morganoliviaevans/cs-147-project/3d-housing/screenshots/Screenshot 2024-11-24 172925.png

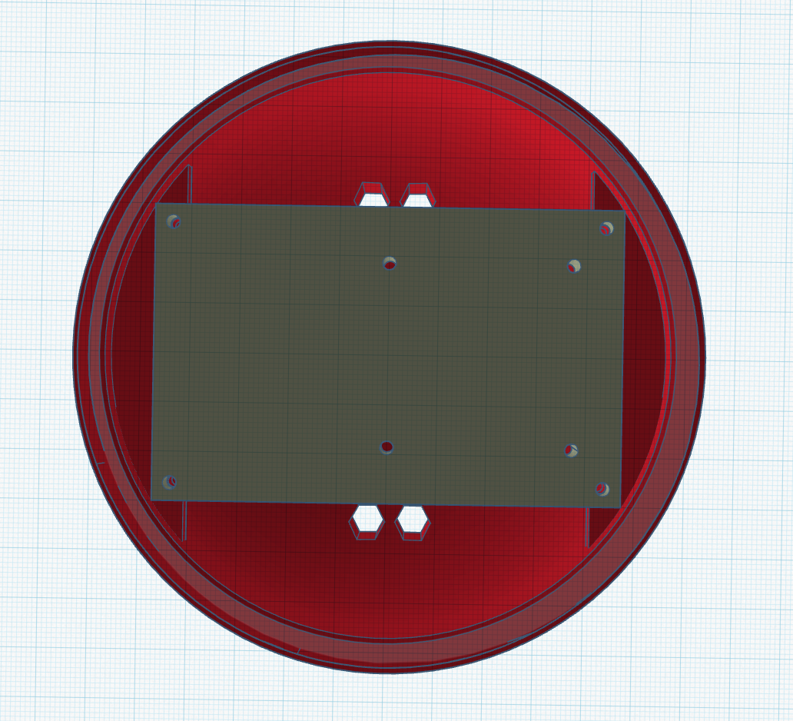
3d-housing/screenshots/Screenshot 2024-11-24 172925.png
