morganoliviaevans/cs-147-project/data-sheets/TTGO-data-sheet.png

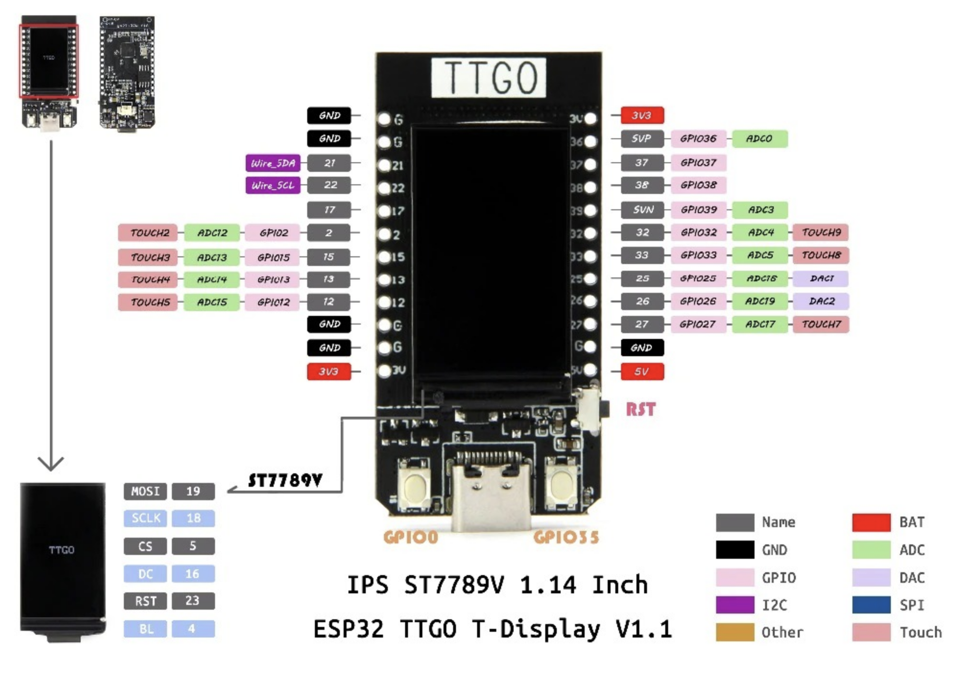
data-sheets/TTGO-data-sheet.png
