morganoliviaevans/cs-147-project/images/aws-graph.png

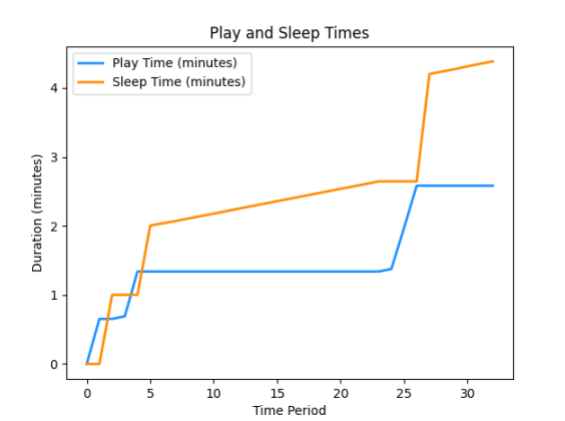
images/aws-graph.png
