morganoliviaevans/cs-147-project/images/aws-off.png

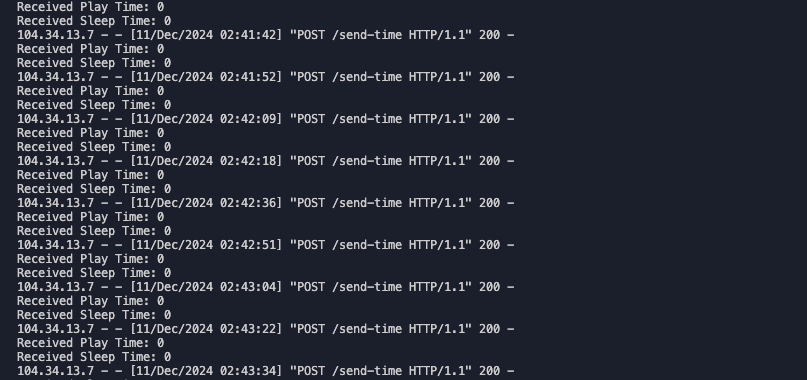
images/aws-off.png
