morganoliviaevans/cs-147-project/images/aws-play.png

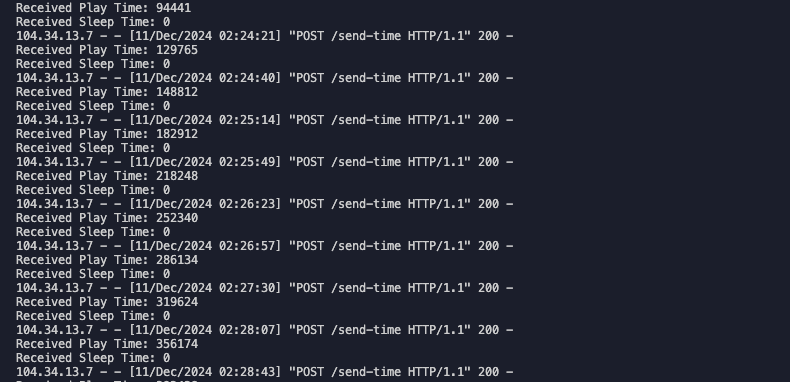
images/aws-play.png
