morganoliviaevans/cs-147-project/images/aws-sleep.png

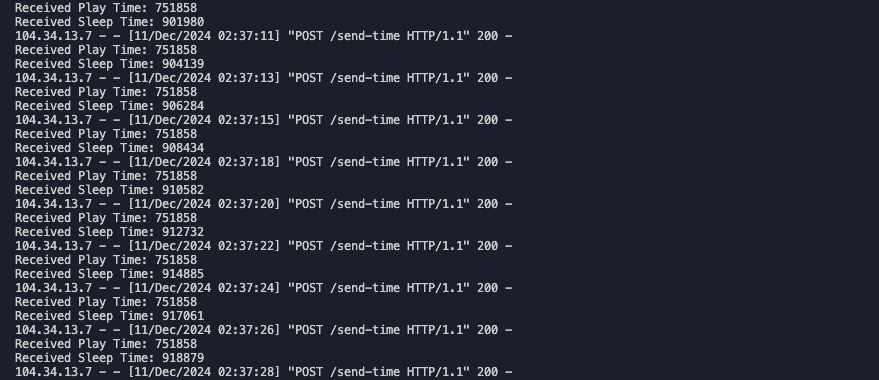
images/aws-sleep.png
