morganoliviaevans/cs-147-project/images/hardware-housing4.png

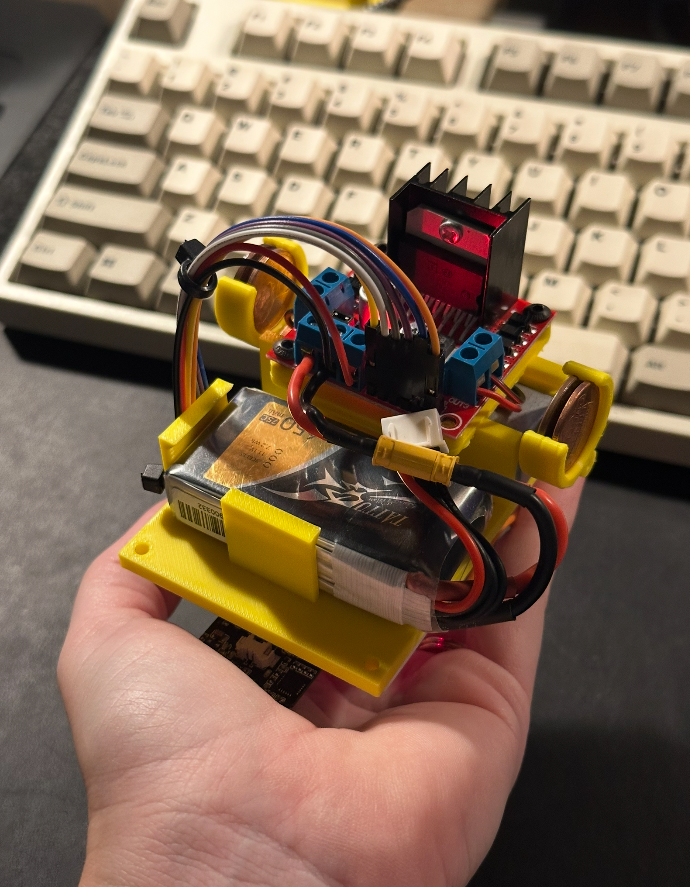
images/hardware-housing4.png
