morganoliviaevans/cs-147-project/images/hardware-housing5.png

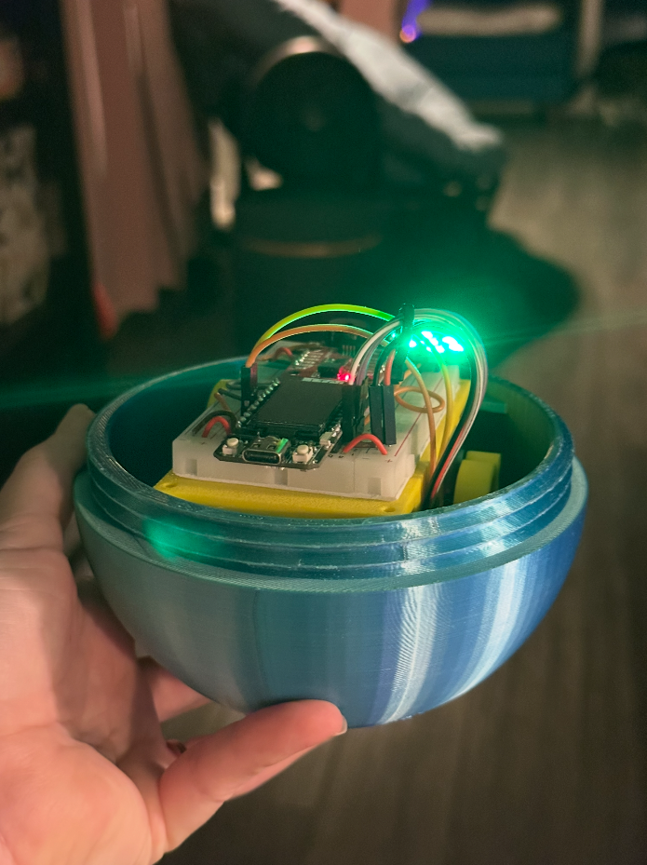
images/hardware-housing5.png
