morganoliviaevans/cs-147-project/3d-housing/298L-holder.stl

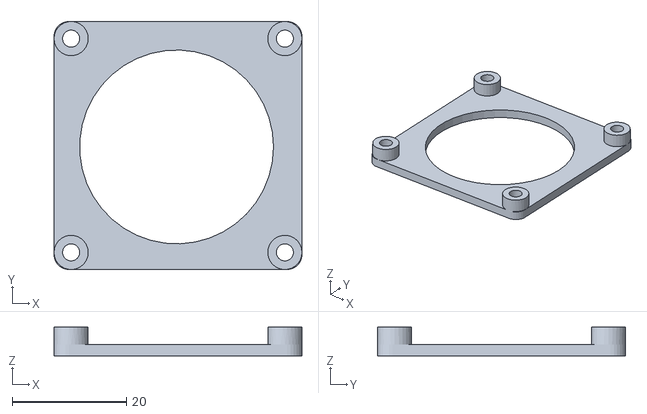
[picture p33: CAD file, 2024-11-27]
3d-housing/298L-holder.stl
43.5 x 43.5 x 5.00
