morganoliviaevans/cs-147-project/3d-housing/sphere-male-raw.stl

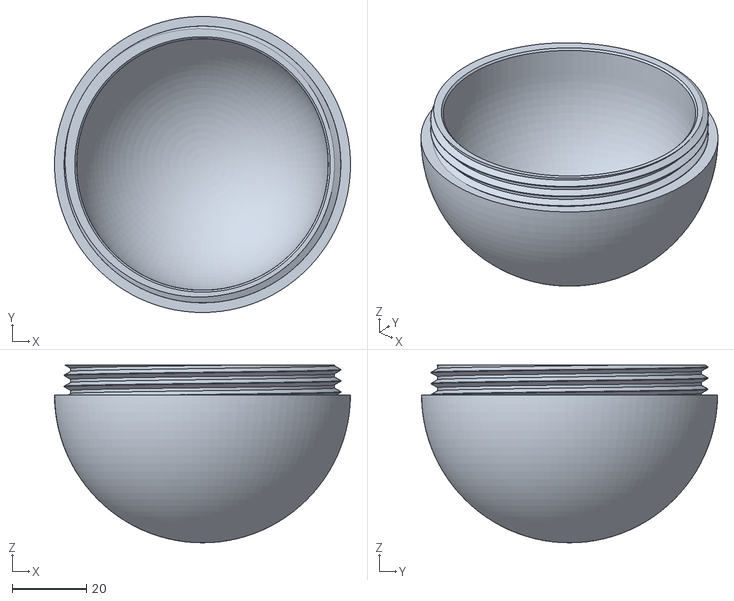
[picture p34: CAD file, 2024-11-27]
3d-housing/sphere-male-raw.stl
80.0 x 80.0 x 48.0
