morganoliviaevans/cs-147-project/3d-housing/130-holder.stl

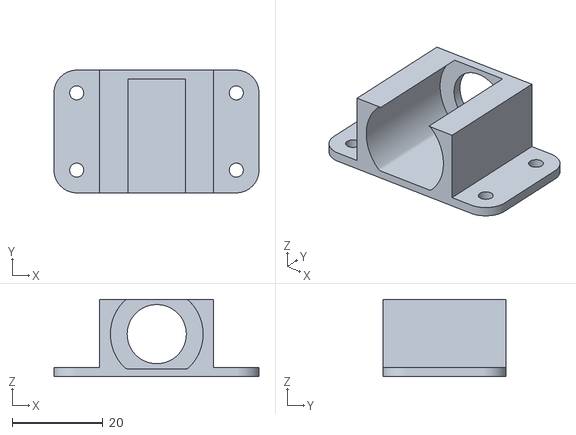
[picture p35: CAD file, 2024-11-27]
3d-housing/130-holder.stl
45.1 x 27.0 x 17.0
