morganoliviaevans/cs-147-project/3d-housing/device-plate-stand.stl

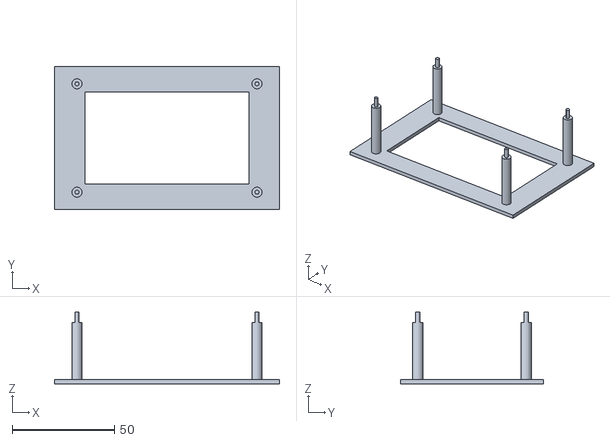
[picture p36: CAD file, 2024-11-27]
3d-housing/device-plate-stand.stl
110.0 x 70.0 x 35.0
