morganoliviaevans/cs-147-project/3d-housing/sphere-female-raw.stl

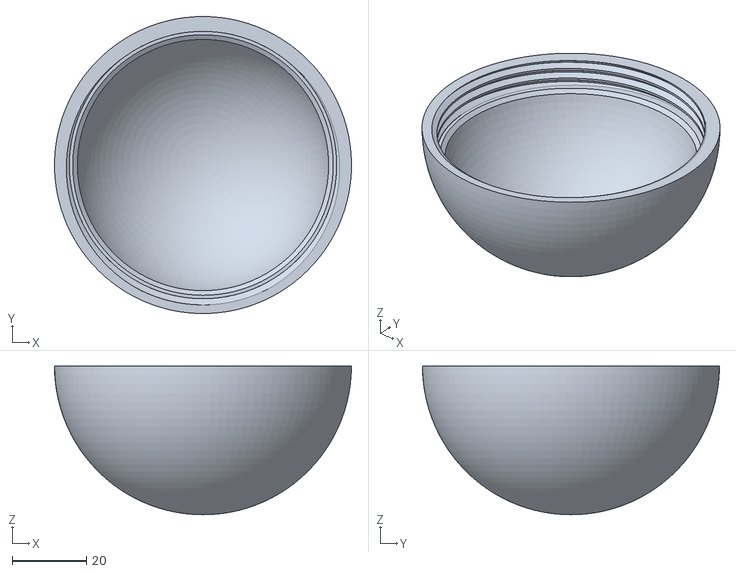
[picture p37: CAD file, 2024-11-27]
3d-housing/sphere-female-raw.stl
80.0 x 80.0 x 40.0
